aliktb/MacroPagePad/HID_KEYPAD/HID_KEYPAD.jpg

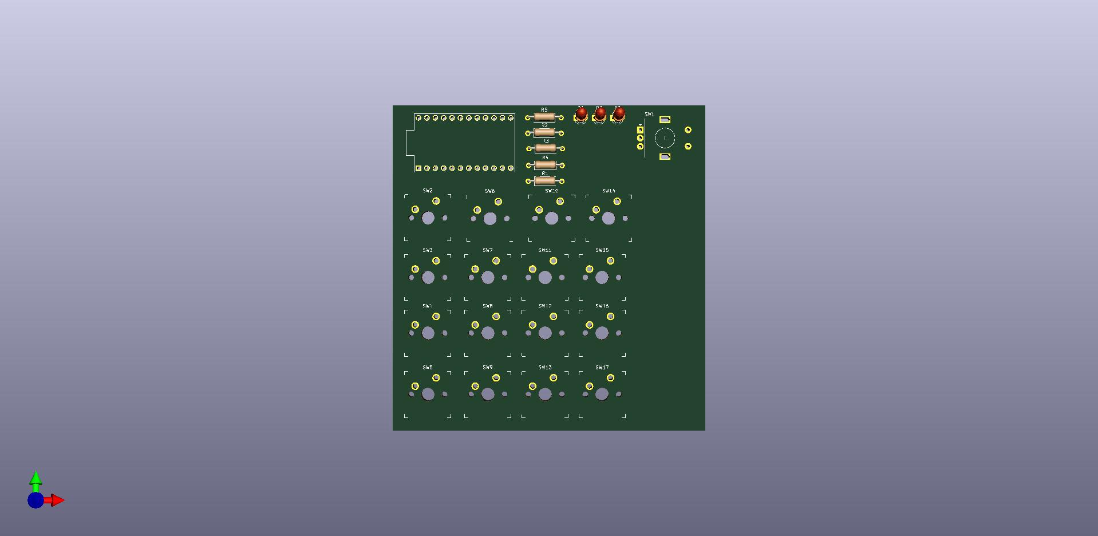
HID_KEYPAD/HID_KEYPAD.jpg
